jpskenn/Jones/assets/DSC_7205.jpeg

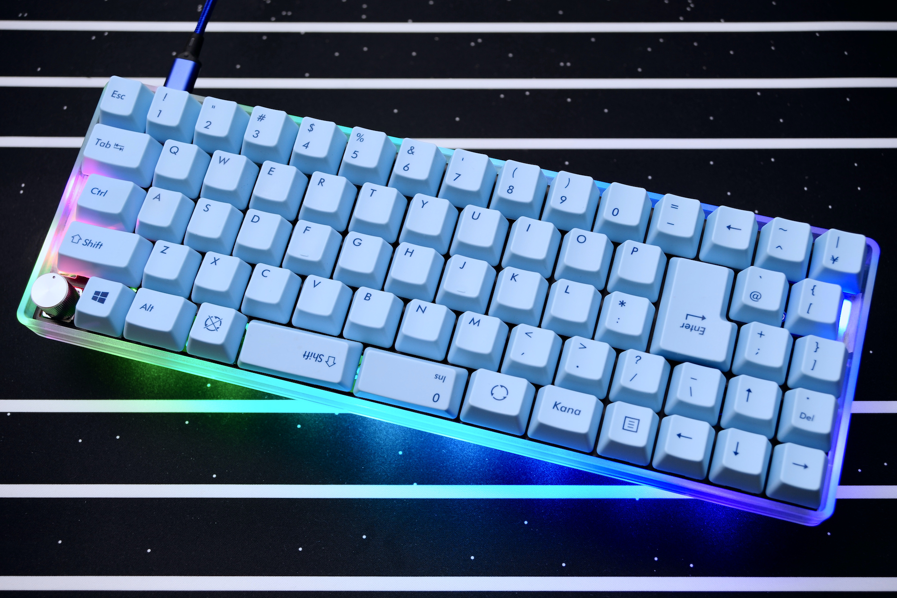
assets/DSC_7205.jpeg
