jpskenn/Jones/assets/DSC_7217.jpeg

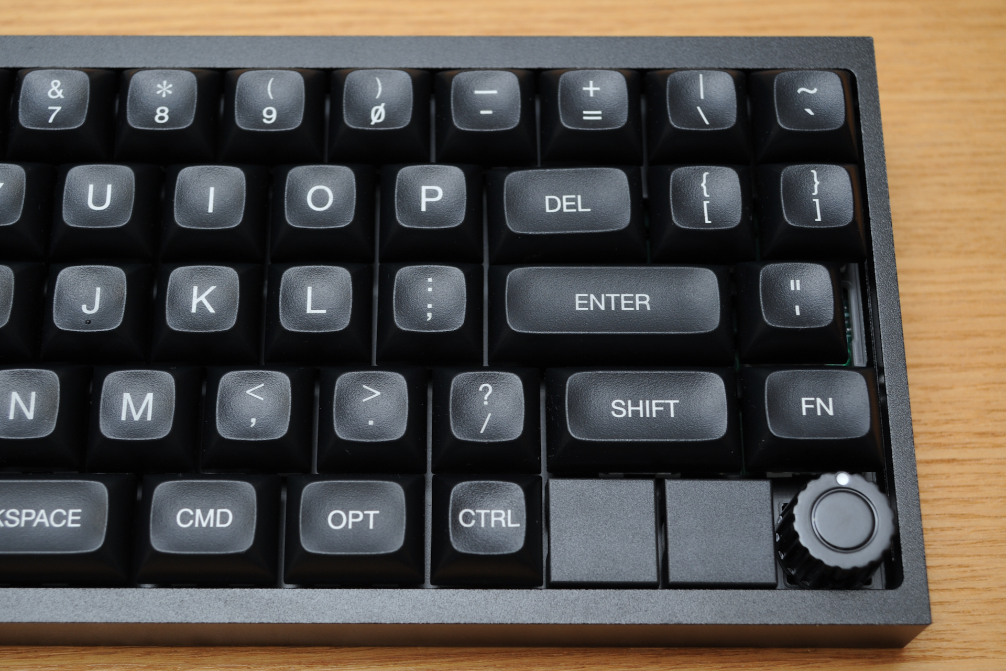
assets/DSC_7217.jpeg
