jpskenn/Jones/assets/IMG_1412.jpeg

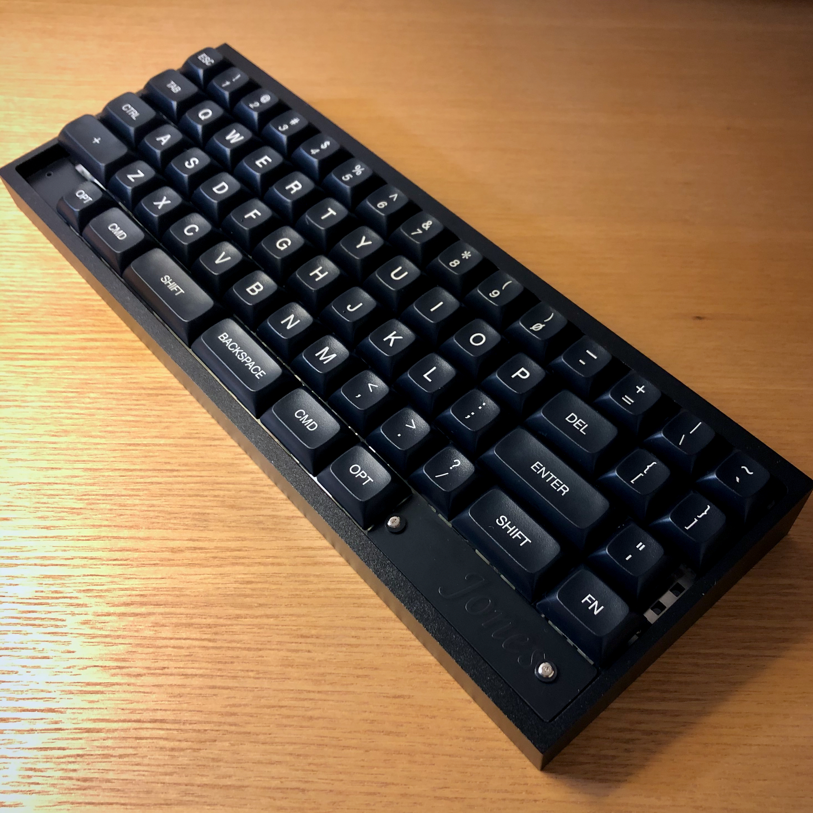
assets/IMG_1412.jpeg
