jpskenn/Jones/assets/IMG_1429.jpeg

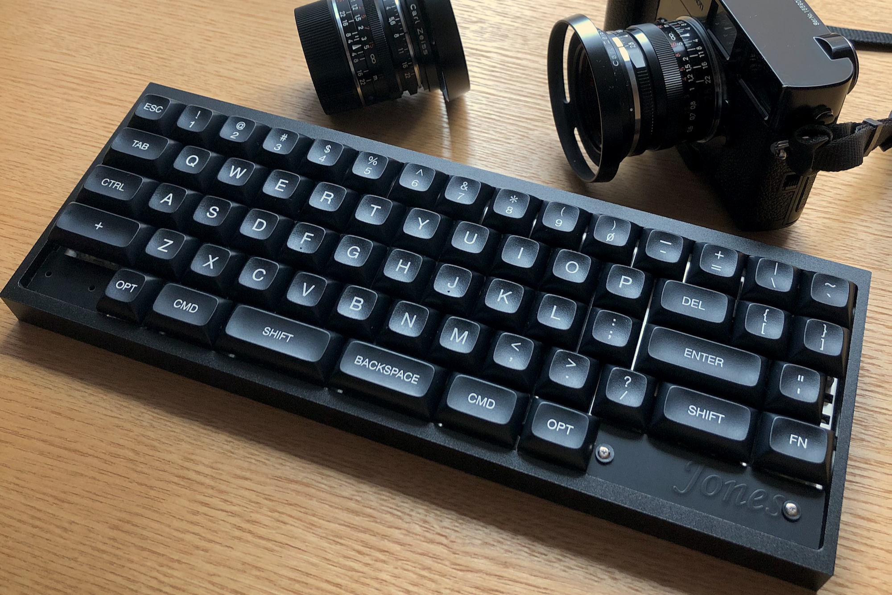
assets/IMG_1429.jpeg
