jpskenn/Jones/assets/IMG_1436.jpeg

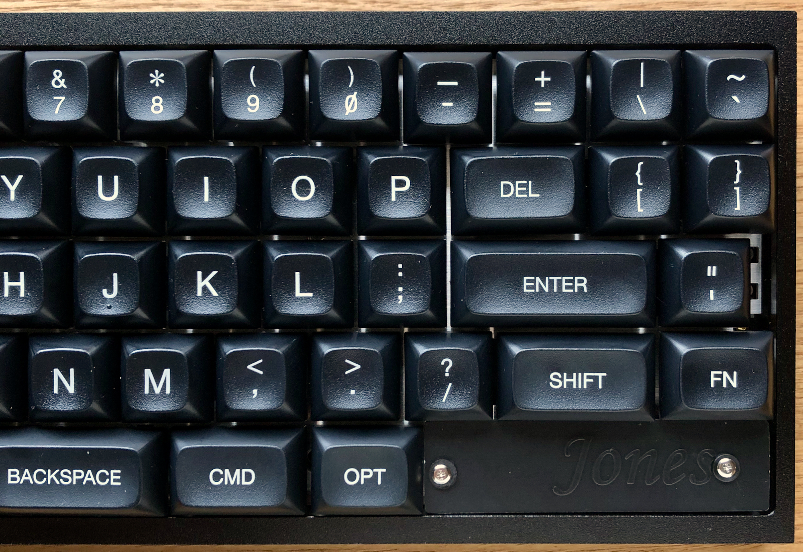
assets/IMG_1436.jpeg
