jpskenn/Jones/assets/IMG_1546.jpeg

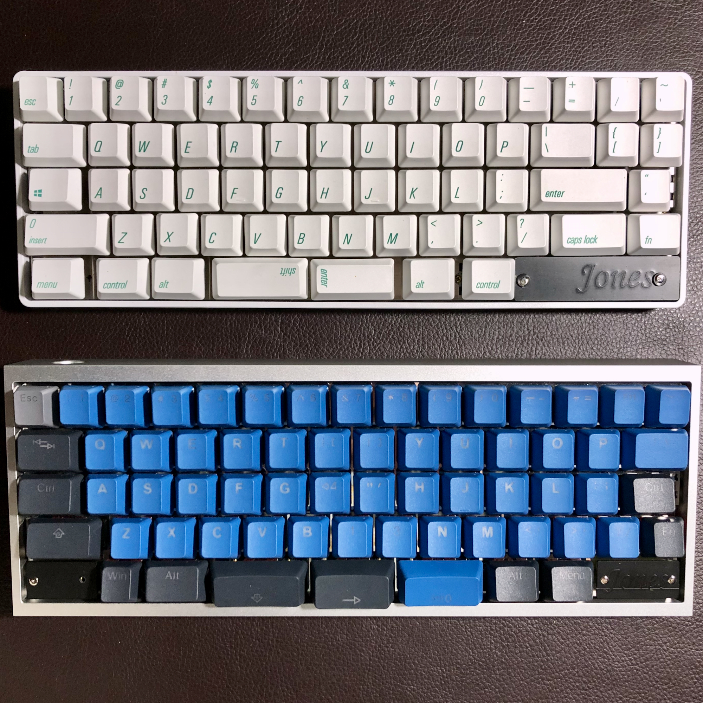
assets/IMG_1546.jpeg
