jpskenn/Jones/assets/jones_layout_v.3.5.4_ANSI.png

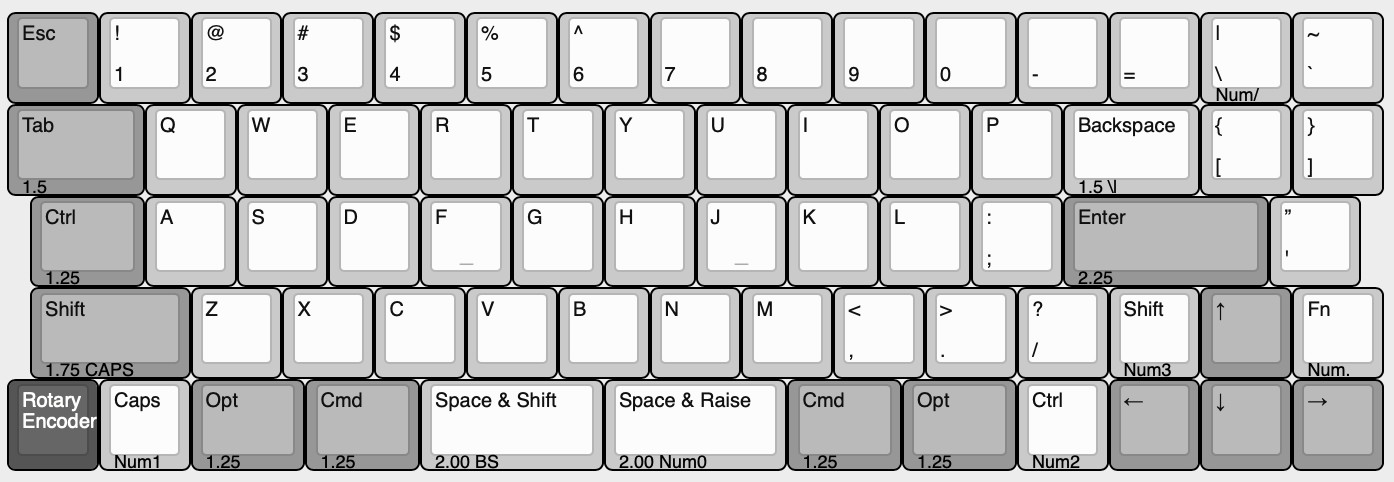
assets/jones_layout_v.3.5.4_ANSI.png
