jpskenn/Jones/assets/jones_layout_v.3.5.4_JP.png

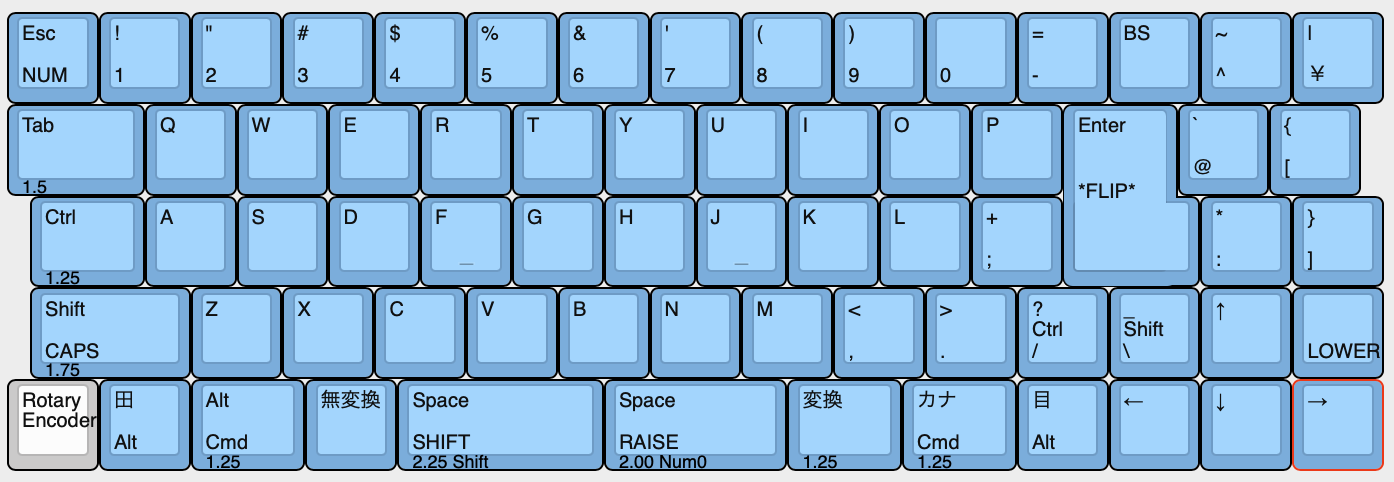
assets/jones_layout_v.3.5.4_JP.png
